msx-solis/MSX-BEER/pictures/fixing_v1.0/IMG_20210903_0205012.jpg

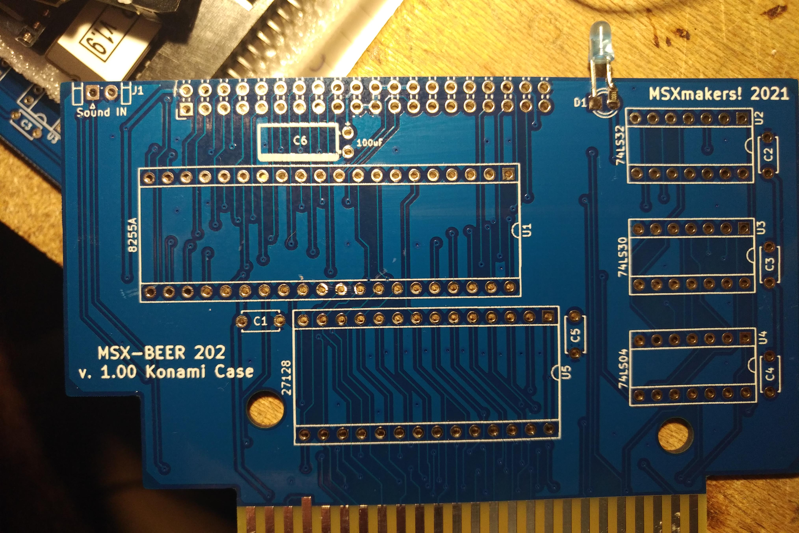
pictures/fixing_v1.0/IMG_20210903_0205012.jpg
