msx-solis/MSX-BEER/pictures/fixing_v1.0/IMG_20210903_0205148.jpg

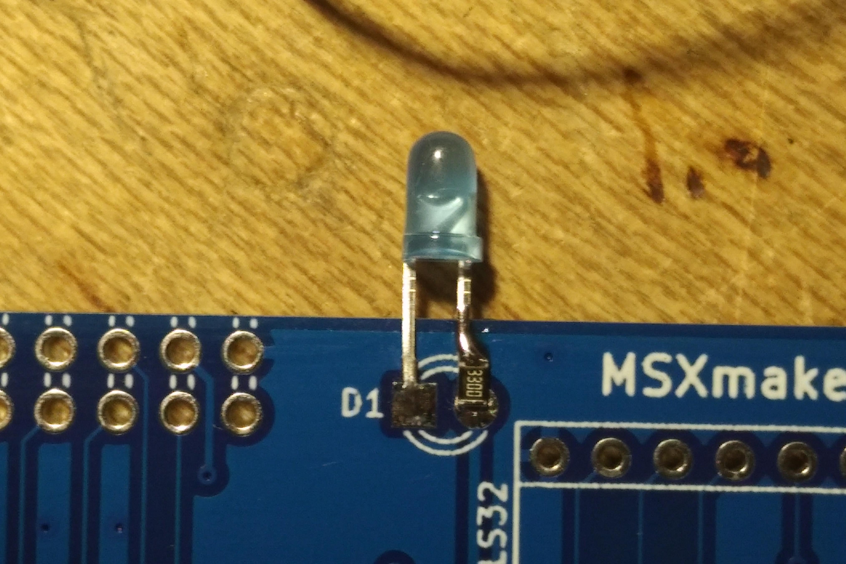
pictures/fixing_v1.0/IMG_20210903_0205148.jpg
