msx-solis/MSX-BEER/pictures/IMG_20230228_2029043.jpg

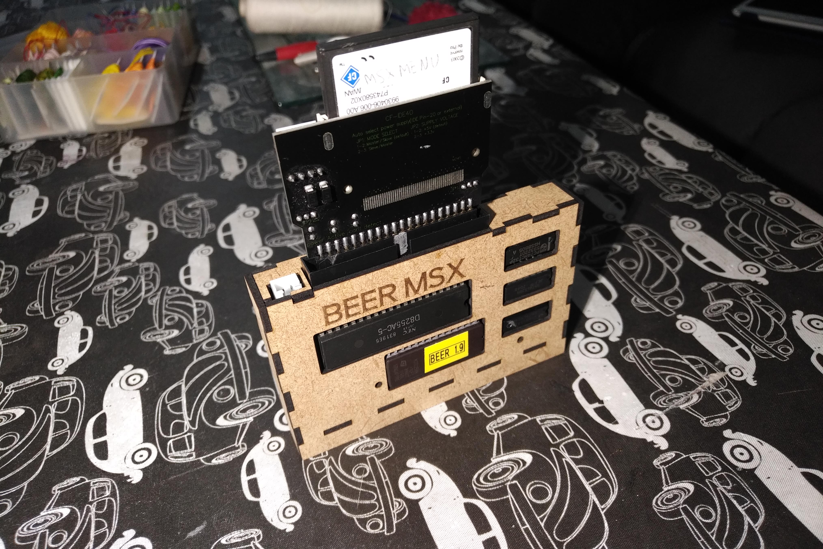
pictures/IMG_20230228_2029043.jpg
