msx-solis/MSX-BEER/pictures/IMG_20230228_2029341.jpg

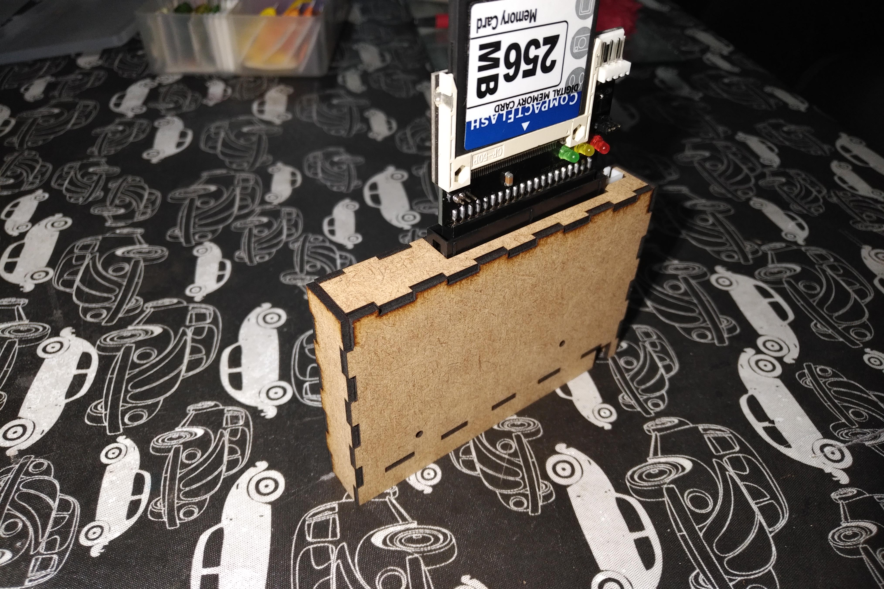
pictures/IMG_20230228_2029341.jpg
